fortinsylvain/MyCpu/Kicad/MyCpu_AddressData.kicad_sch

## KiCad design Kicad/MyCpu_AddressData.kicad_sch (2025-06-30)

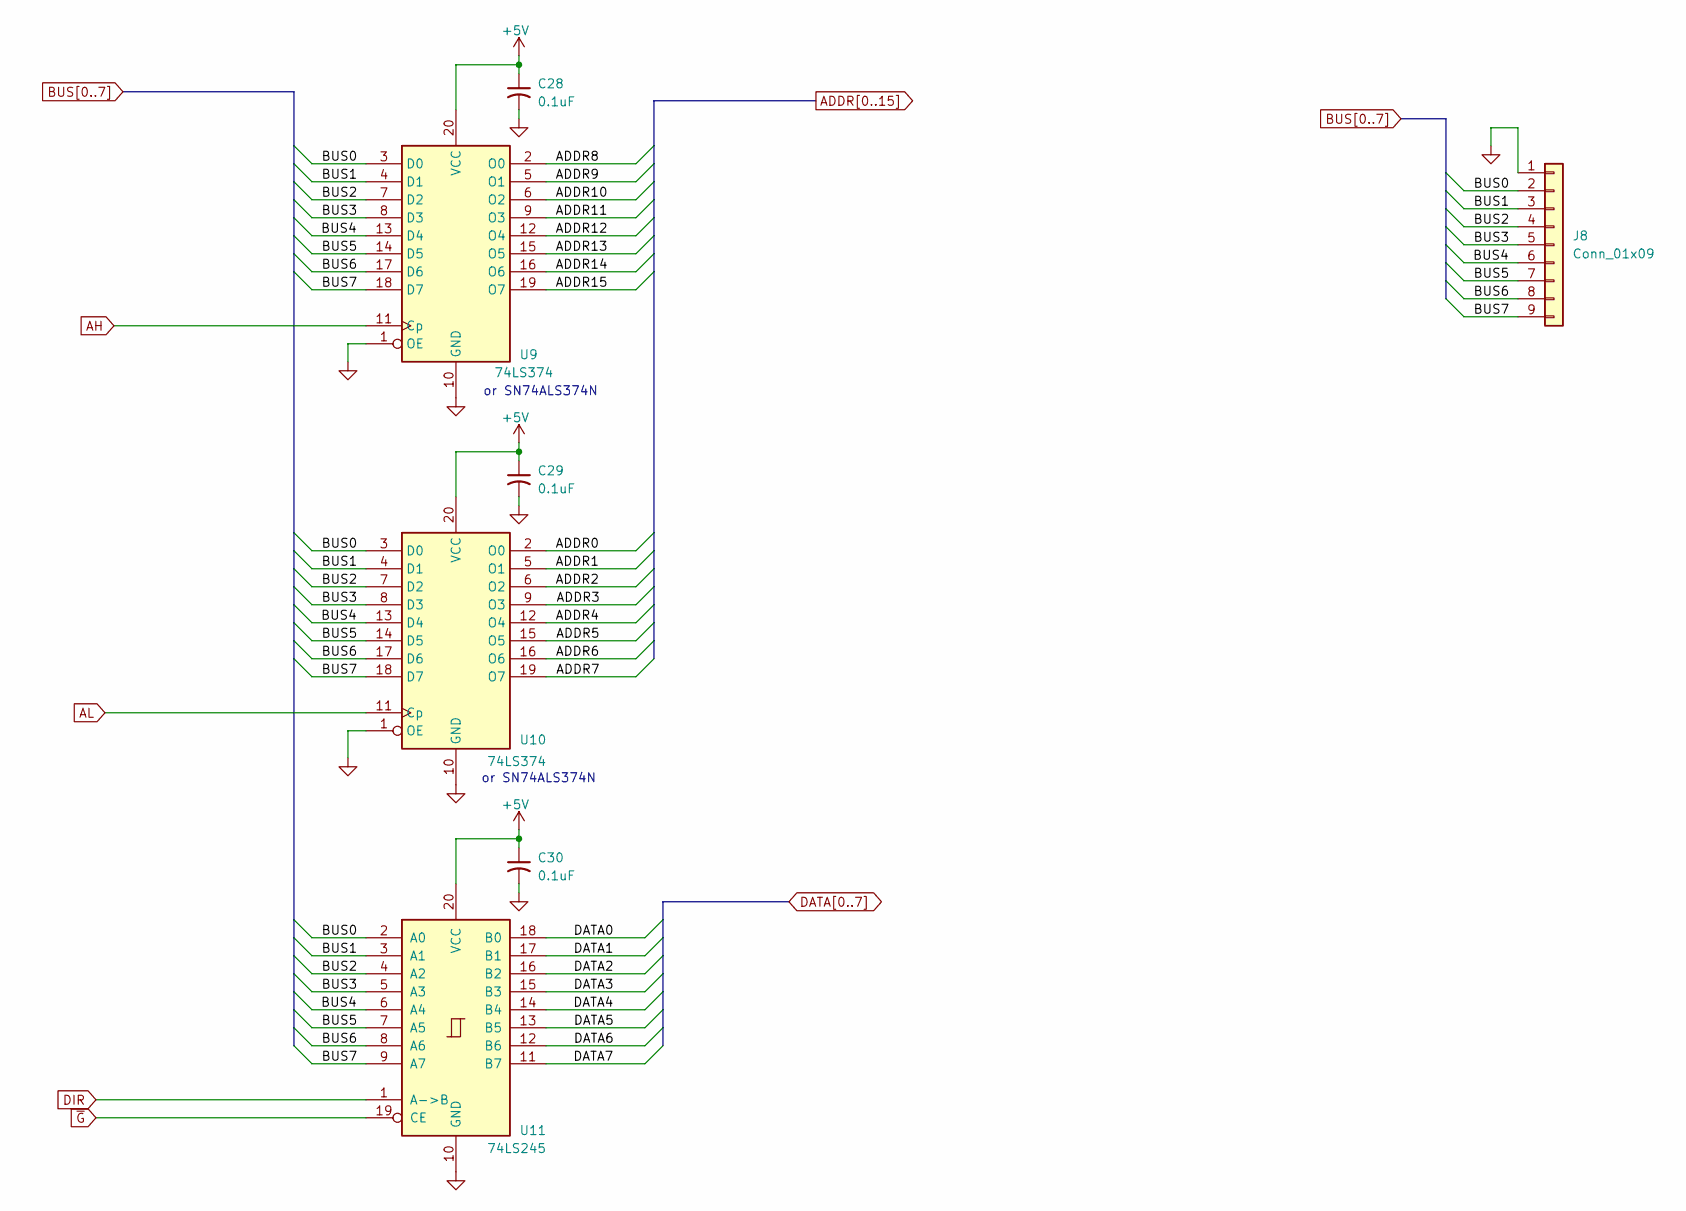
[picture p20: schematic MyCpu_AddressData.kicad_sch]

Parts:
C28, C29, C30: 0.1uF; C_Disc_D6.0mm_W2.5mm_P5.00mm
J8: Conn_01x09; PinHeader_1x09_P2.54mm_Vertical
U9, U10: 74LS374; DIP-20_W7.62mm_Socket_LongPads
U11: 74LS245; DIP-20_W7.62mm_Socket_LongPads

Connections:
+5V: C28.1, C29.1, C30.1, U9.20 (VCC), U10.20 (VCC), U11.20 (VCC)
ADDR0: U10.2 (O0)
ADDR1: U10.5 (O1)
ADDR2: U10.6 (O2)
ADDR3: U10.9 (O3)
ADDR4: U10.12 (O4)
ADDR5: U10.15 (O5)
ADDR6: U10.16 (O6)
ADDR7: U10.19 (O7)
ADDR8: U9.2 (O0)
ADDR9: U9.5 (O1)
ADDR10: U9.6 (O2)
ADDR11: U9.9 (O3)
ADDR12: U9.12 (O4)
ADDR13: U9.15 (O5)
ADDR14: U9.16 (O6)
ADDR15: U9.19 (O7)
AH: U9.11 (Cp)
AL: U10.11 (Cp)
BUS0: J8.2, U9.3 (D0), U10.3 (D0), U11.2 (A0)
BUS1: J8.3, U9.4 (D1), U10.4 (D1), U11.3 (A1)
BUS2: J8.4, U9.7 (D2), U10.7 (D2), U11.4 (A2)
BUS3: J8.5, U9.8 (D3), U10.8 (D3), U11.5 (A3)
BUS4: J8.6, U9.13 (D4), U10.13 (D4), U11.6 (A4)
BUS5: J8.7, U9.14 (D5), U10.14 (D5), U11.7 (A5)
BUS6: J8.8, U9.17 (D6), U10.17 (D6), U11.8 (A6)
BUS7: J8.9, U9.18 (D7), U10.18 (D7), U11.9 (A7)
DATA0: U11.18 (B0)
DATA1: U11.17 (B1)
DATA2: U11.16 (B2)
DATA3: U11.15 (B3)
DATA4: U11.14 (B4)
DATA5: U11.13 (B5)
DATA6: U11.12 (B6)
DATA7: U11.11 (B7)
DIR: U11.1 (A->B)
GND: C28.2, C29.2, C30.2, J8.1, U9.1 (OE), U9.10 (GND), U10.1 (OE), U10.10 (GND), U11.10 (GND)
~G: U11.19 (CE)

Notes on the sheet:
or SN74ALS374N
