fortinsylvain/MyCpu/Kicad/MyCpu_Alu.kicad_sch

## KiCad design Kicad/MyCpu_Alu.kicad_sch (2025-06-30)

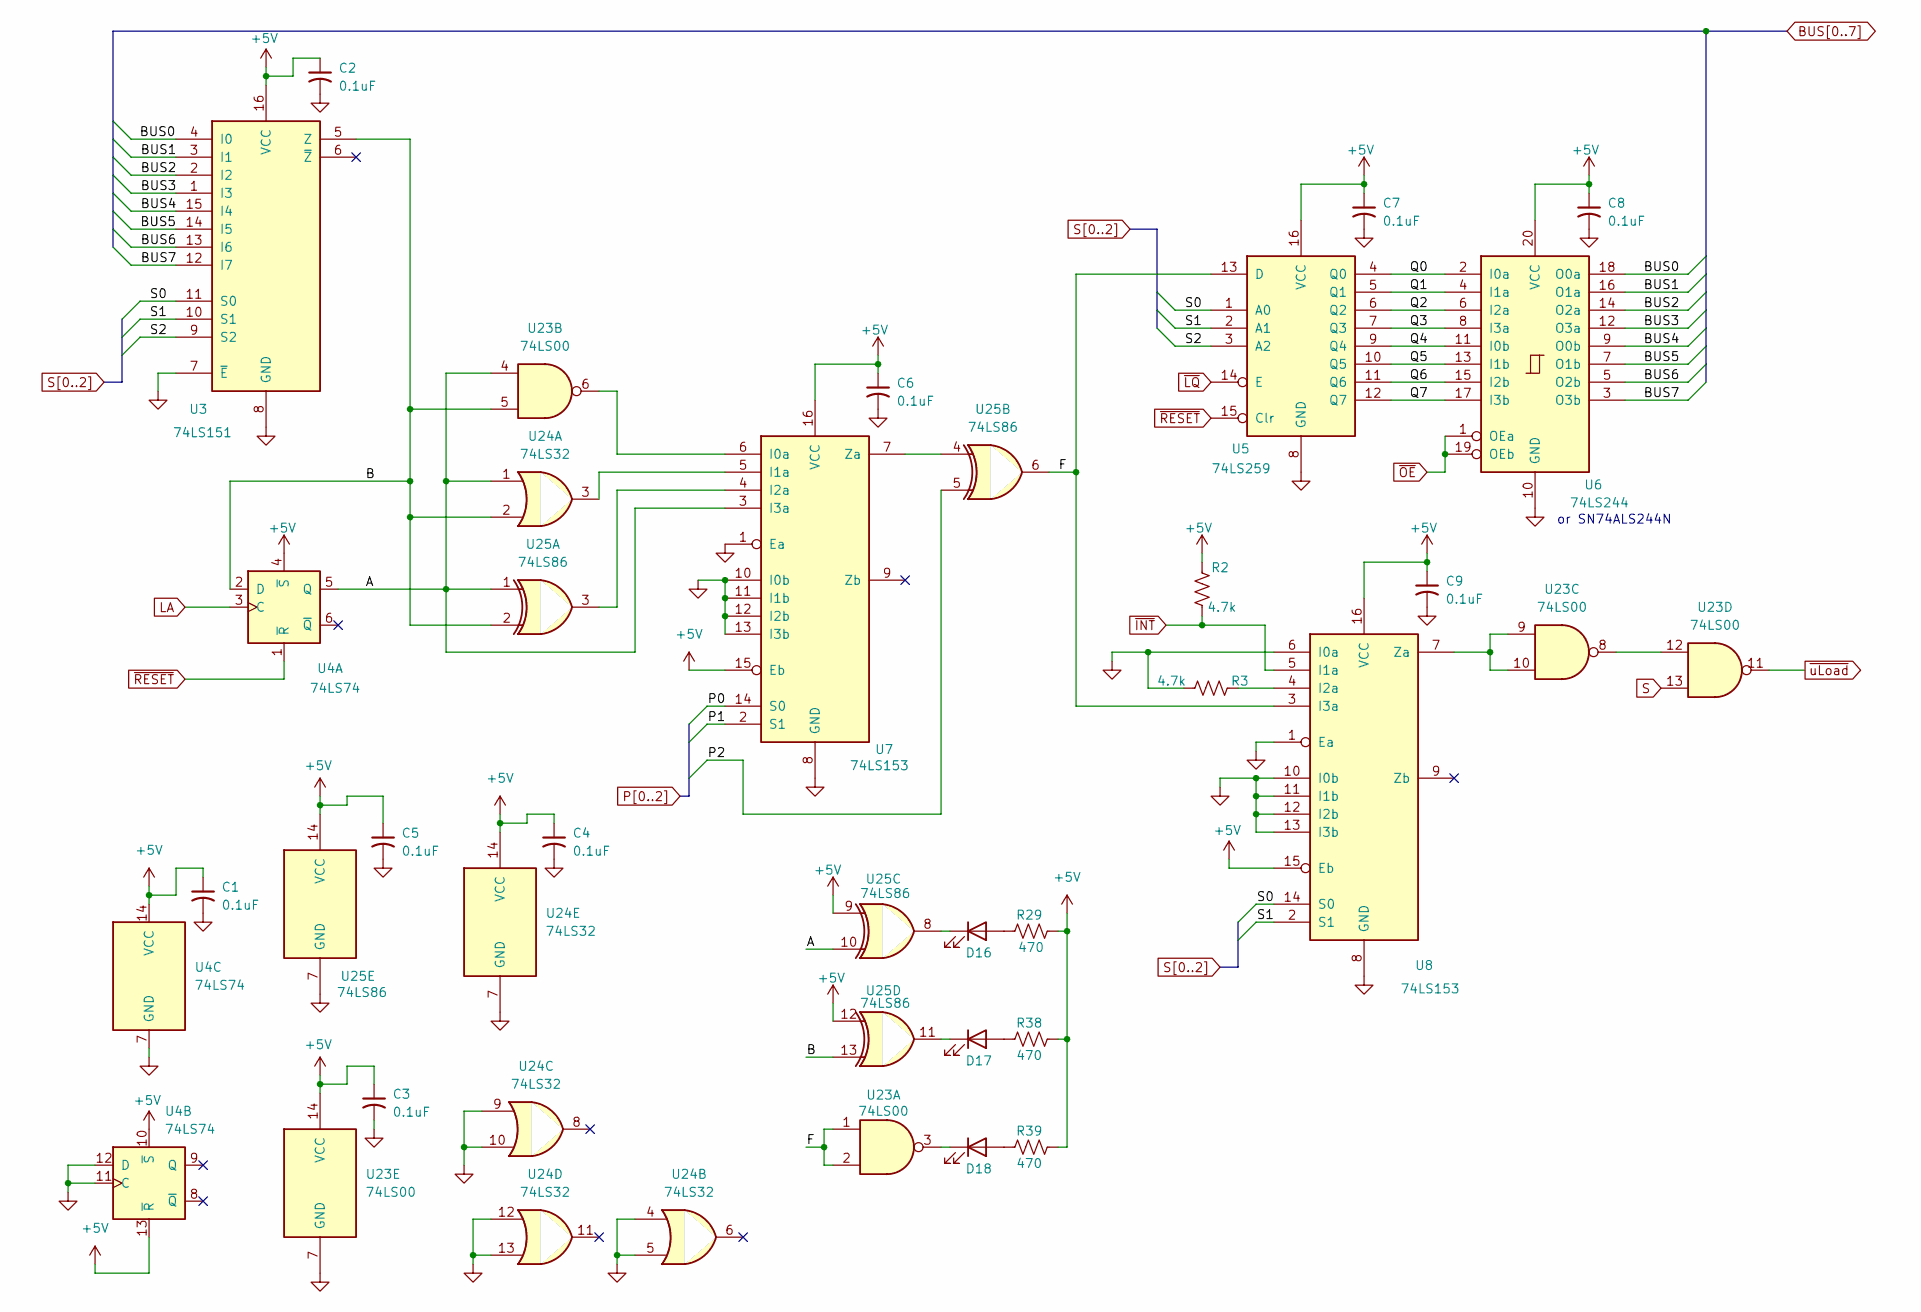
[picture p21: schematic MyCpu_Alu.kicad_sch]

Parts:
C1, C2, C3, C4, C5, C6, C7, C8, C9: 0.1uF; C_Disc_D6.0mm_W2.5mm_P5.00mm
D16, D17, D18: LED; LED_D5.0mm
R2, R3: 4.7k; R_Axial_DIN0207_L6.3mm_D2.5mm_P2.54mm_Vertical
R29, R38, R39: 470; R_Axial_DIN0207_L6.3mm_D2.5mm_P2.54mm_Vertical
U3: 74LS151; DIP-16_W7.62mm_Socket_LongPads
U4: 74LS74; DIP-14_W7.62mm_Socket_LongPads
U5: 74LS259; DIP-16_W7.62mm_Socket_LongPads
U6: 74LS244; DIP-20_W7.62mm_Socket_LongPads
U7, U8: 74LS153; DIP-16_W7.62mm_Socket_LongPads
U23: 74LS00; DIP-14_W7.62mm_Socket_LongPads
U24: 74LS32; DIP-14_W7.62mm_Socket_LongPads
U25: 74LS86; DIP-14_W7.62mm_Socket_LongPads

Connections:
+5V: C1.1, C2.1, C3.1, C4.1, C5.1, C6.1, C7.1, C8.1, C9.1, R2.1, R29.1, R38.1, R39.1, U3.16 (VCC), U4.4 (~S), U4.10 (~S), U4.13 (~R), U4.14 (VCC), U5.16 (VCC), U6.20 (VCC), U7.15 (Eb), U7.16 (VCC), U8.15 (Eb), U8.16 (VCC), U23.14 (VCC), U24.14 (VCC), U25.9, U25.12, U25.14 (VCC)
A: U4.5 (Q), U7.3 (I3a), U23.4, U24.1, U25.1, U25.10
B: U3.5 (Z), U4.2 (D), U23.5, U24.2, U25.2, U25.13
BUS0: U3.4 (I0), U6.18 (O0a)
BUS1: U3.3 (I1), U6.16 (O1a)
BUS2: U3.2 (I2), U6.14 (O2a)
BUS3: U3.1 (I3), U6.12 (O3a)
BUS4: U3.15 (I4), U6.9 (O0b)
BUS5: U3.14 (I5), U6.7 (O1b)
BUS6: U3.13 (I6), U6.5 (O2b)
BUS7: U3.12 (I7), U6.3 (O3b)
F: U5.13 (D), U8.3 (I3a), U23.1, U23.2, U25.6
GND: C1.2, C2.2, C3.2, C4.2, C5.2, C6.2, C7.2, C8.2, C9.2, R3.1, U3.7 (~E), U3.8 (GND), U4.7 (GND), U4.11 (C), U4.12 (D), U5.8 (GND), U6.10 (GND), U7.1 (Ea), U7.8 (GND), U7.10 (I0b), U7.11 (I1b), U7.12 (I2b), U7.13 (I3b), U8.1 (Ea), U8.6 (I0a), U8.8 (GND), U8.10 (I0b), U8.11 (I1b), U8.12 (I2b), U8.13 (I3b), U23.7 (GND), U24.4, U24.5, U24.7 (GND), U24.9, U24.10, U24.12, U24.13, U25.7 (GND)
LA: U4.3 (C)
unnamed: D16.1 (K), U25.8
unnamed: D16.2 (A), R29.2
unnamed: D17.1 (K), U25.11
unnamed: D17.2 (A), R38.2
unnamed: D18.1 (K), U23.3
unnamed: D18.2 (A), R39.2
unnamed: R3.2, U8.4 (I2a)
unnamed: U7.6 (I0a), U23.6
unnamed: U8.7 (Za), U23.9, U23.10
unnamed: U23.8, U23.12
unnamed: U7.5 (I1a), U24.3
unnamed: U7.4 (I2a), U25.3
unnamed: U7.7 (Za), U25.4
P0: U7.14 (S0)
P1: U7.2 (S1)
P2: U25.5
Q0: U5.4 (Q0), U6.2 (I0a)
Q1: U5.5 (Q1), U6.4 (I1a)
Q2: U5.6 (Q2), U6.6 (I2a)
Q3: U5.7 (Q3), U6.8 (I3a)
Q4: U5.9 (Q4), U6.11 (I0b)
Q5: U5.10 (Q5), U6.13 (I1b)
Q6: U5.11 (Q6), U6.15 (I2b)
Q7: U5.12 (Q7), U6.17 (I3b)
S: U23.13
S0: U3.11 (S0), U5.1 (A0), U8.14 (S0)
S1: U3.10 (S1), U5.2 (A1), U8.2 (S1)
S2: U3.9 (S2), U5.3 (A2)
~INT: R2.2, U8.5 (I1a)
~LQ: U5.14 (E)
~OE: U6.1 (OEa), U6.19 (OEb)
~RESET: U4.1 (~R), U5.15 (Clr)
~uLoad: U23.11

Notes on the sheet:
or SN74ALS244N
