fortinsylvain/MyCpu/Kicad/MyCpu_Clock.kicad_sch

## KiCad design Kicad/MyCpu_Clock.kicad_sch (2025-06-30)

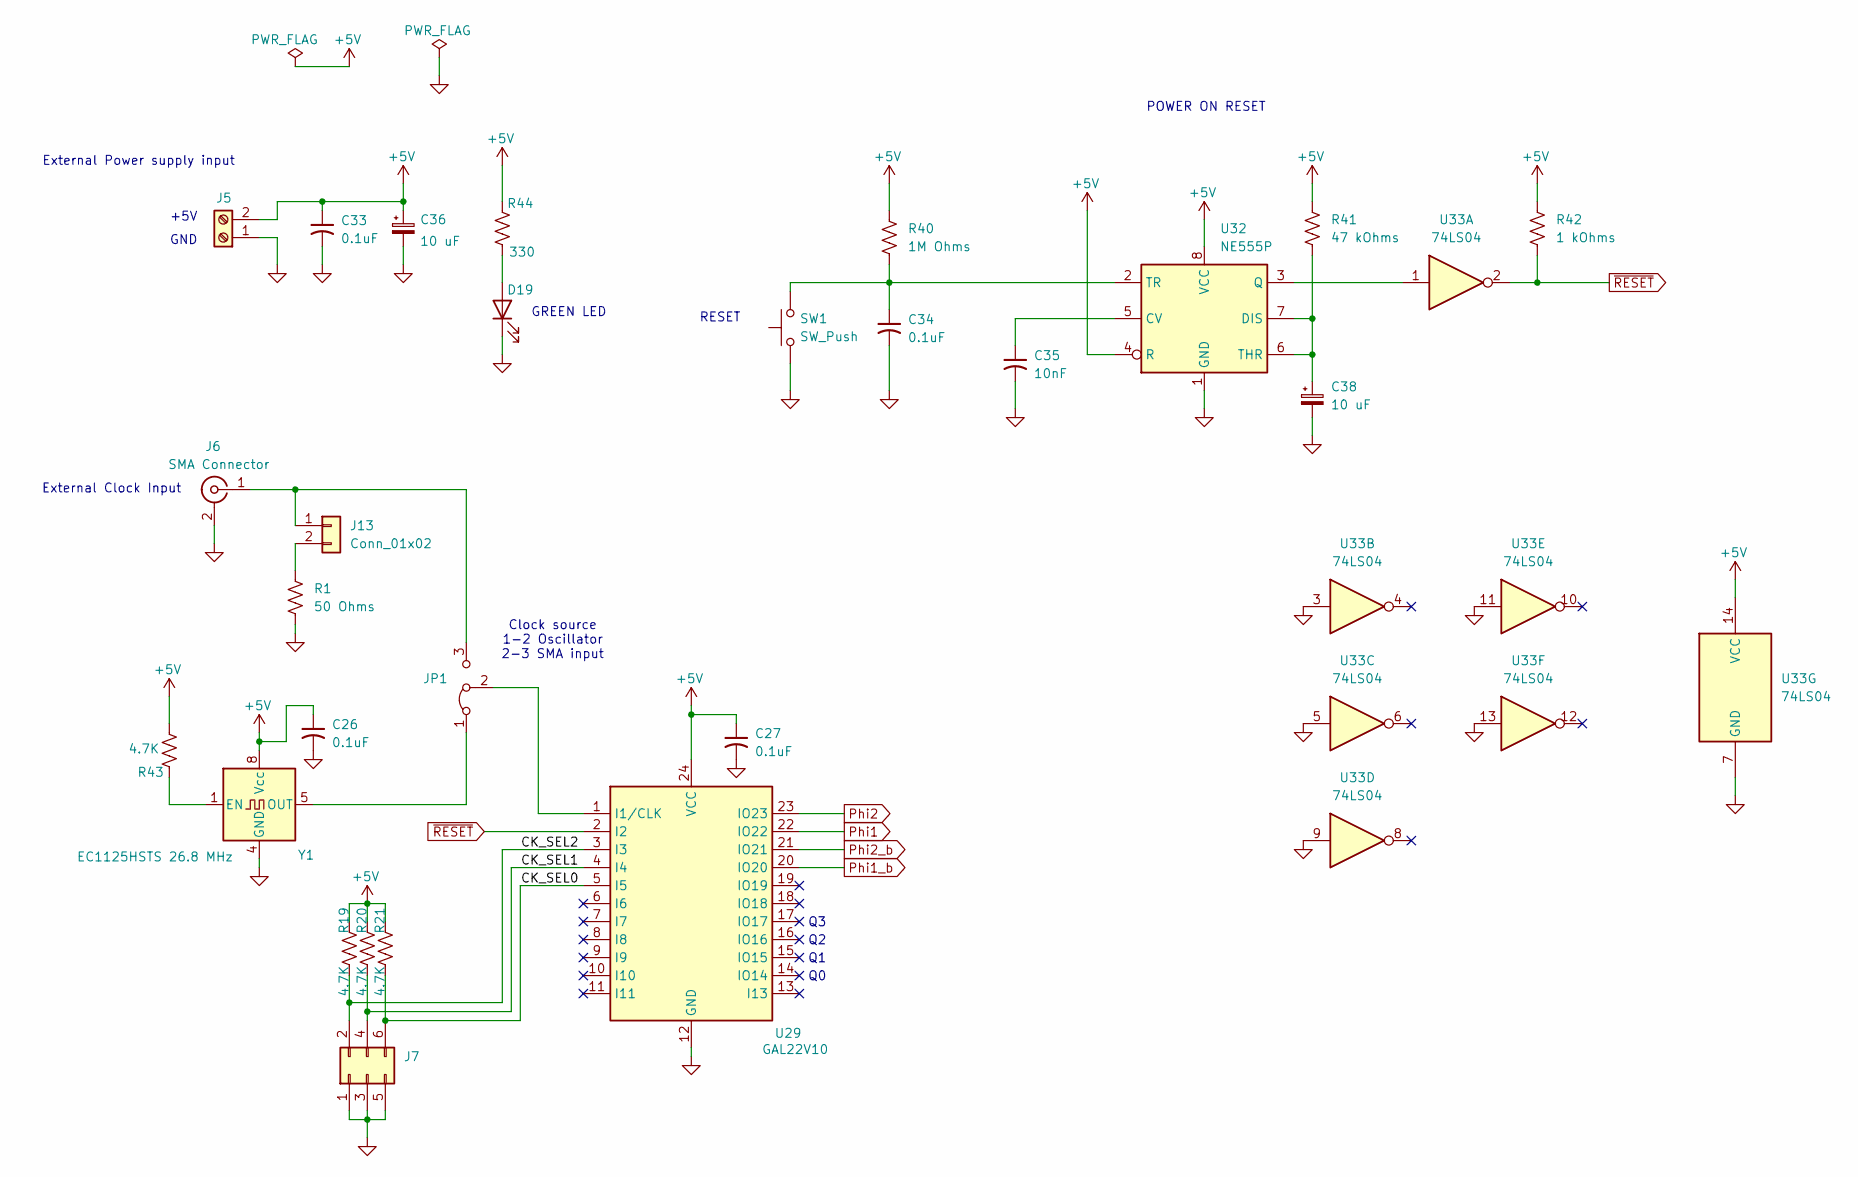
[picture p22: schematic MyCpu_Clock.kicad_sch]

Parts:
C26, C27, C33, C34: 0.1uF; C_Disc_D6.0mm_W2.5mm_P5.00mm
C35: 10nF; C_Disc_D6.5mm_W2.1mm_P6.50mm
C36, C38: 10 uF; CP_Radial_D5.0mm_P2.50mm
D19: LED; LED_D5.0mm
J5: Screw_Terminal_01x02; TerminalBlock_CUI_TB007-508-02_1x02_P5.08mm_Horizontal
J6: SMA Connector; GSG-SMA-73251-2120_drill_0.5mm
J7: Conn_02x03_Odd_Even; PinHeader_2x03_P2.54mm_Vertical
J13: Conn_01x02; PinHeader_1x02_P2.54mm_Vertical
JP1: Jumper_3_Bridged12; PinHeader_1x03_P2.54mm_Vertical
R1: 50 Ohms; R_Axial_DIN0207_L6.3mm_D2.5mm_P2.54mm_Vertical
R19, R20, R21, R43: 4.7K; R_Axial_DIN0207_L6.3mm_D2.5mm_P2.54mm_Vertical
R40: 1M Ohms; R_Axial_DIN0207_L6.3mm_D2.5mm_P2.54mm_Vertical
R41: 47 kOhms; R_Axial_DIN0207_L6.3mm_D2.5mm_P2.54mm_Vertical
R42: 1 kOhms; R_Axial_DIN0207_L6.3mm_D2.5mm_P2.54mm_Vertical
R44: 330; R_Axial_DIN0207_L6.3mm_D2.5mm_P2.54mm_Vertical
SW1: SW_Push; SW_PUSH-12mm
U29: GAL22V10; DIP-24_W7.62mm_Socket_LongPads
U32: NE555P; DIP-8_W7.62mm_Socket_LongPads
U33: 74LS04; DIP-14_W7.62mm_Socket_LongPads
Y1: EC1125HSTS 26.8 MHz; Oscillator_DIP-8

Connections:
+5V: C26.1, C27.1, C33.1, C36.1, J5.2, R19.1, R20.1, R21.1, R40.1, R41.1, R42.1, R43.1, R44.1, U29.24 (VCC), U32.4 (R), U32.8 (VCC), U33.14 (VCC), Y1.8 (Vcc)
CK_SEL0: J7.6, R21.2, U29.5 (I5)
CK_SEL1: J7.4, R20.2, U29.4 (I4)
CK_SEL2: J7.2, R19.2, U29.3 (I3)
GND: C26.2, C27.2, C33.2, C34.2, C35.2, C36.2, C38.2, D19.1 (K), J5.1, J6.2 (Ext), J7.1, J7.3, J7.5, R1.2, SW1.1, U29.12 (GND), U32.1 (GND), U33.3, U33.5, U33.7 (GND), U33.9, U33.11, U33.13, Y1.4 (GND)
unnamed: C34.1, R40.2, SW1.2, U32.2 (TR)
unnamed: C35.1, U32.5 (CV)
unnamed: C38.1, R41.2, U32.6 (THR), U32.7 (DIS)
unnamed: D19.2 (A), R44.2
unnamed: J6.1 (In), J13.1, JP1.3 (B)
unnamed: J13.2, R1.1
unnamed: JP1.1 (A), Y1.5 (OUT)
unnamed: JP1.2 (C), U29.1 (I1/CLK)
unnamed: R43.2, Y1.1 (EN)
unnamed: U32.3 (Q), U33.1
Phi1: U29.22 (IO22)
Phi1_b: U29.20 (IO20)
Phi2: U29.23 (IO23)
Phi2_b: U29.21 (IO21)
~RESET: R42.2, U29.2 (I2), U33.2

Notes on the sheet:
RESET
POWER ON RESET
GREEN LED
External Clock Input
+5V
GND
Clock source 1-2 Oscillator 2-3 SMA input
External Power supply input
