fortinsylvain/MyCpu/Kicad/MyCpu_EEPROM_ucode.kicad_sch

## KiCad design Kicad/MyCpu_EEPROM_ucode.kicad_sch (2025-06-30)

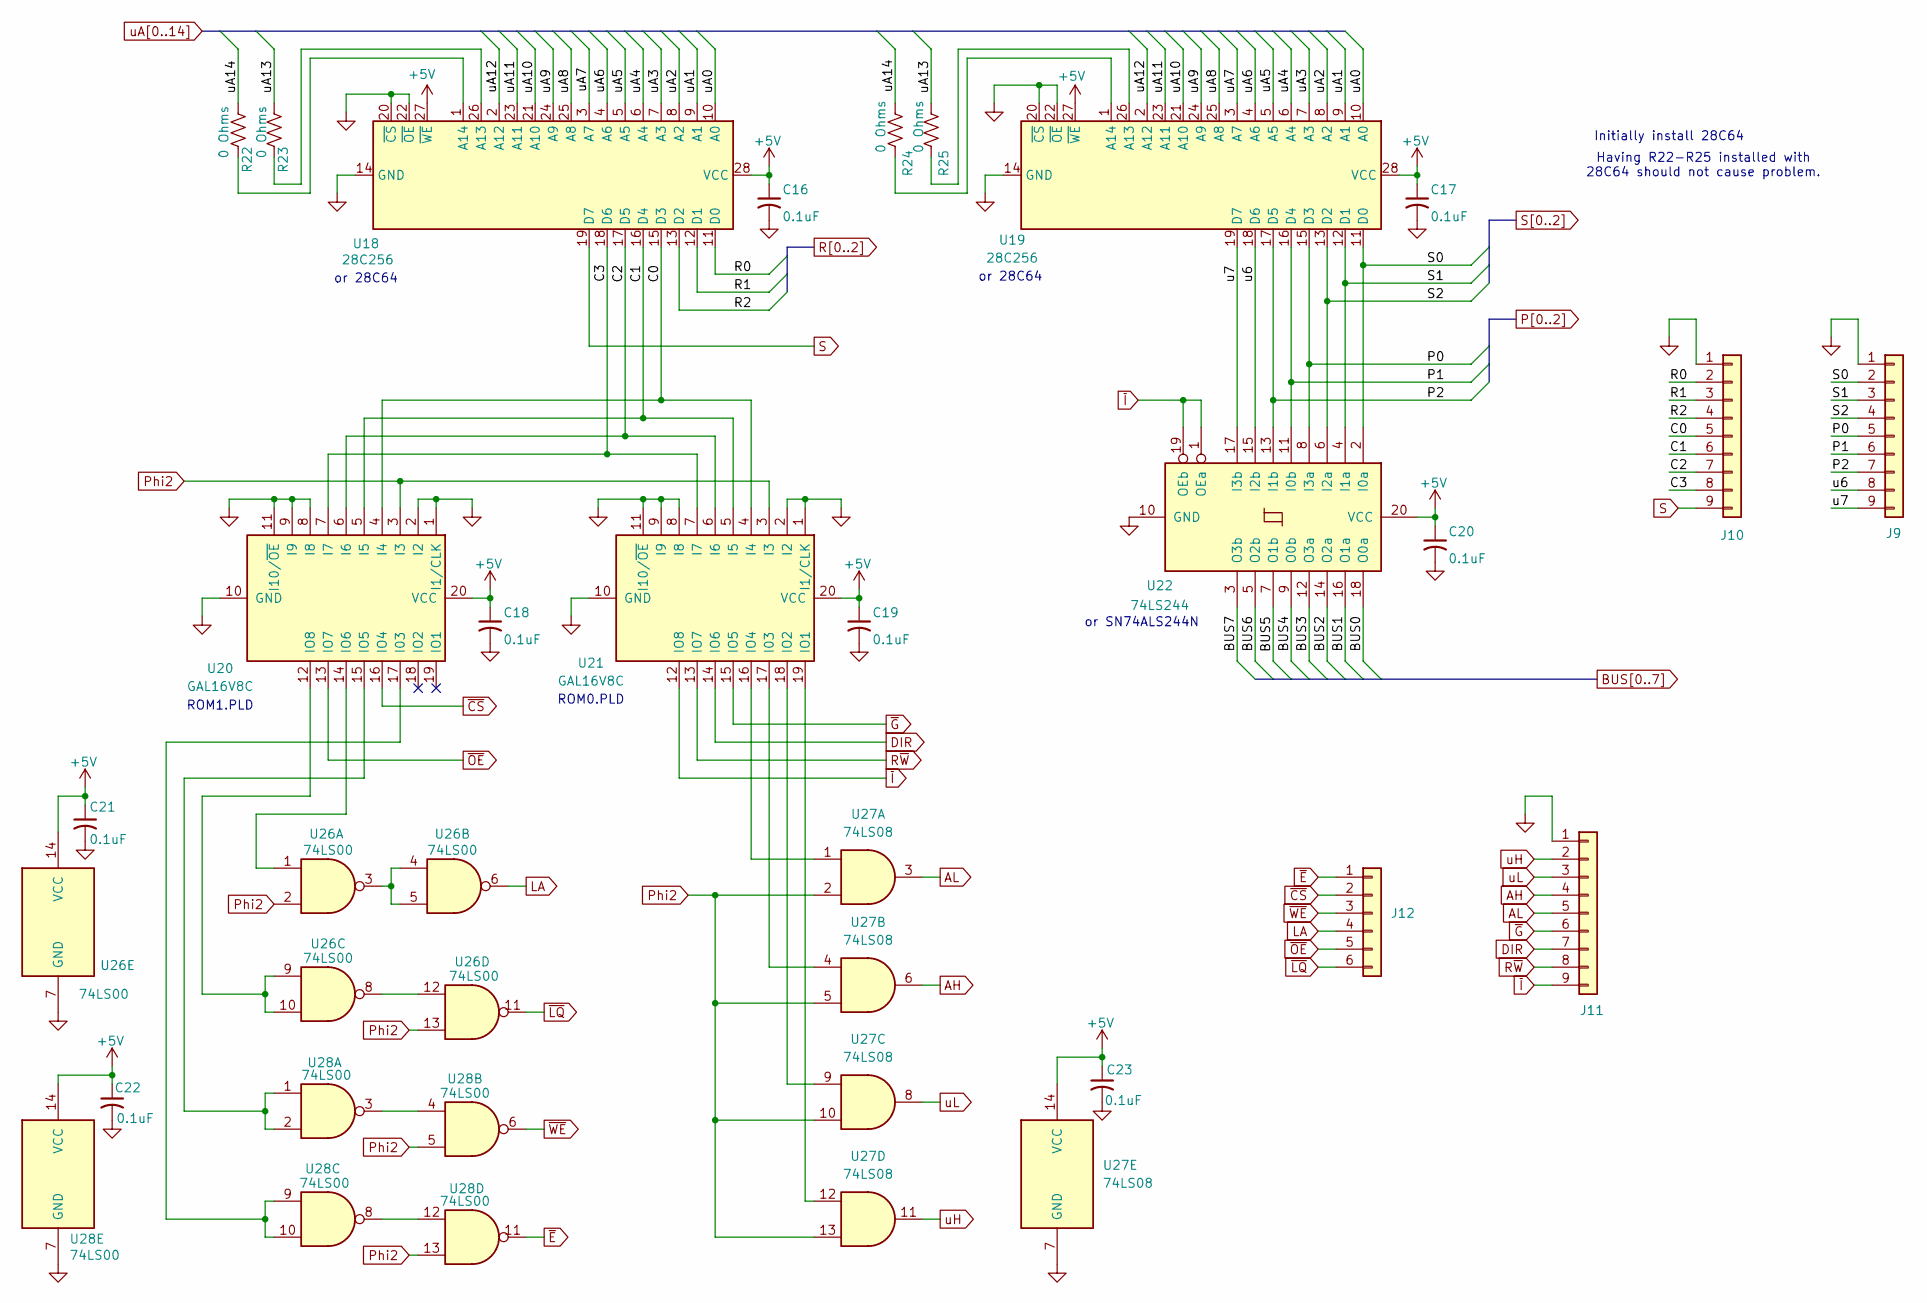
[picture p23: schematic MyCpu_EEPROM_ucode.kicad_sch]

Parts:
C16, C17, C18, C19, C20, C21, C22, C23: 0.1uF; C_Disc_D6.0mm_W2.5mm_P5.00mm
J9, J10, J11: Conn_01x09; PinHeader_1x09_P2.54mm_Vertical
J12: Conn_01x06; PinHeader_1x06_P2.54mm_Vertical
R22, R23, R24, R25: 0 Ohms; R_0603_1608Metric_Pad0.98x0.95mm_HandSolder
U18, U19: 28C256; DIP-28_W15.24mm_Socket_LongPads
U20, U21: GAL16V8C; DIP-20_W7.62mm_Socket_LongPads
U22: 74LS244; DIP-20_W7.62mm_Socket_LongPads
U26, U28: 74LS00; DIP-14_W7.62mm_Socket_LongPads
U27: 74LS08; DIP-14_W7.62mm_Socket_LongPads

Connections:
+5V: C16.1, C17.1, C18.1, C19.1, C20.1, C21.1, C22.1, C23.1, U18.27 (~WE), U18.28 (VCC), U19.27 (~WE), U19.28 (VCC), U20.20 (VCC), U21.20 (VCC), U22.20 (VCC), U26.14 (VCC), U27.14 (VCC), U28.14 (VCC)
AH: J11.4, U27.6
AL: J11.5, U27.3
BUS0: U22.18 (O0a)
BUS1: U22.16 (O1a)
BUS2: U22.14 (O2a)
BUS3: U22.12 (O3a)
BUS4: U22.9 (O0b)
BUS5: U22.7 (O1b)
BUS6: U22.5 (O2b)
BUS7: U22.3 (O3b)
C0: J10.5, U18.15 (D3), U20.4 (I4), U21.4 (I4)
C1: J10.6, U18.16 (D4), U20.5 (I5), U21.5 (I5)
C2: J10.7, U18.17 (D5), U20.6 (I6), U21.6 (I6)
C3: J10.8, U18.18 (D6), U20.7 (I7), U21.7 (I7)
DIR: J11.7, U21.14 (IO6)
GND: C16.2, C17.2, C18.2, C19.2, C20.2, C21.2, C22.2, C23.2, J9.1, J10.1, J11.1, U18.14 (GND), U18.20 (~CS), U18.22 (~OE), U19.14 (GND), U19.20 (~CS), U19.22 (~OE), U20.1 (I1/CLK), U20.2 (I2), U20.8 (I8), U20.9 (I9), U20.10 (GND), U20.11 (I10/~OE), U21.1 (I1/CLK), U21.2 (I2), U21.8 (I8), U21.9 (I9), U21.10 (GND), U21.11 (I10/~OE), U22.10 (GND), U26.7 (GND), U27.7 (GND), U28.7 (GND)
LA: J12.4, U26.6
unnamed: R22.2, U18.1 (A14)
unnamed: R23.2, U18.26 (A13)
unnamed: R24.2, U19.1 (A14)
unnamed: R25.2, U19.26 (A13)
unnamed: U20.12 (IO8), U26.9, U26.10
unnamed: U20.14 (IO6), U26.1
unnamed: U20.15 (IO5), U28.1, U28.2
unnamed: U20.17 (I03), U28.9, U28.10
unnamed: U21.16 (IO4), U27.1
unnamed: U21.17 (I03), U27.4
unnamed: U21.18 (IO2), U27.9
unnamed: U21.19 (IO1), U27.12
unnamed: U26.3, U26.4, U26.5
unnamed: U26.8, U26.12
unnamed: U28.3, U28.4
unnamed: U28.8, U28.12
P0: J9.5, U19.15 (D3), U22.8 (I3a)
P1: J9.6, U19.16 (D4), U22.11 (I0b)
P2: J9.7, U19.17 (D5), U22.13 (I1b)
Phi2: U20.3 (I3), U21.3 (I3), U26.2, U26.13, U27.2, U27.5, U27.10, U27.13, U28.5, U28.13
R0: J10.2, U18.11 (D0)
R1: J10.3, U18.12 (D1)
R2: J10.4, U18.13 (D2)
R~W: J11.8, U21.13 (IO7)
S: J10.9, U18.19 (D7)
S0: J9.2, U19.11 (D0), U22.2 (I0a)
S1: J9.3, U19.12 (D1), U22.4 (I1a)
S2: J9.4, U19.13 (D2), U22.6 (I2a)
u6: J9.8, U19.18 (D6), U22.15 (I2b)
u7: J9.9, U19.19 (D7), U22.17 (I3b)
uA0: U18.10 (A0), U19.10 (A0)
uA1: U18.9 (A1), U19.9 (A1)
uA2: U18.8 (A2), U19.8 (A2)
uA3: U18.7 (A3), U19.7 (A3)
uA4: U18.6 (A4), U19.6 (A4)
uA5: U18.5 (A5), U19.5 (A5)
uA6: U18.4 (A6), U19.4 (A6)
uA7: U18.3 (A7), U19.3 (A7)
uA8: U18.25 (A8), U19.25 (A8)
uA9: U18.24 (A9), U19.24 (A9)
uA10: U18.21 (A10), U19.21 (A10)
uA11: U18.23 (A11), U19.23 (A11)
uA12: U18.2 (A12), U19.2 (A12)
uA13: R23.1, R25.1
uA14: R22.1, R24.1
uH: J11.2, U27.11
uL: J11.3, U27.8
~CS: J12.2, U20.16 (IO4)
~E: J12.1, U28.11
~G: J11.6, U21.15 (IO5)
~I: J11.9, U21.12 (IO8), U22.1 (OEa), U22.19 (OEb)
~LQ: J12.6, U26.11
~OE: J12.5, U20.13 (IO7)
~WE: J12.3, U28.6

Notes on the sheet:
Initially install 28C64
ROM0.PLD
Having R22-R25 installed with 28C64 should not cause problem.
ROM1.PLD
or 28C64
or SN74ALS244N
