fortinsylvain/MyCpu/Kicad/MyCpu_ProgramRamEeprom.kicad_sch

## KiCad design Kicad/MyCpu_ProgramRamEeprom.kicad_sch (2025-06-30)

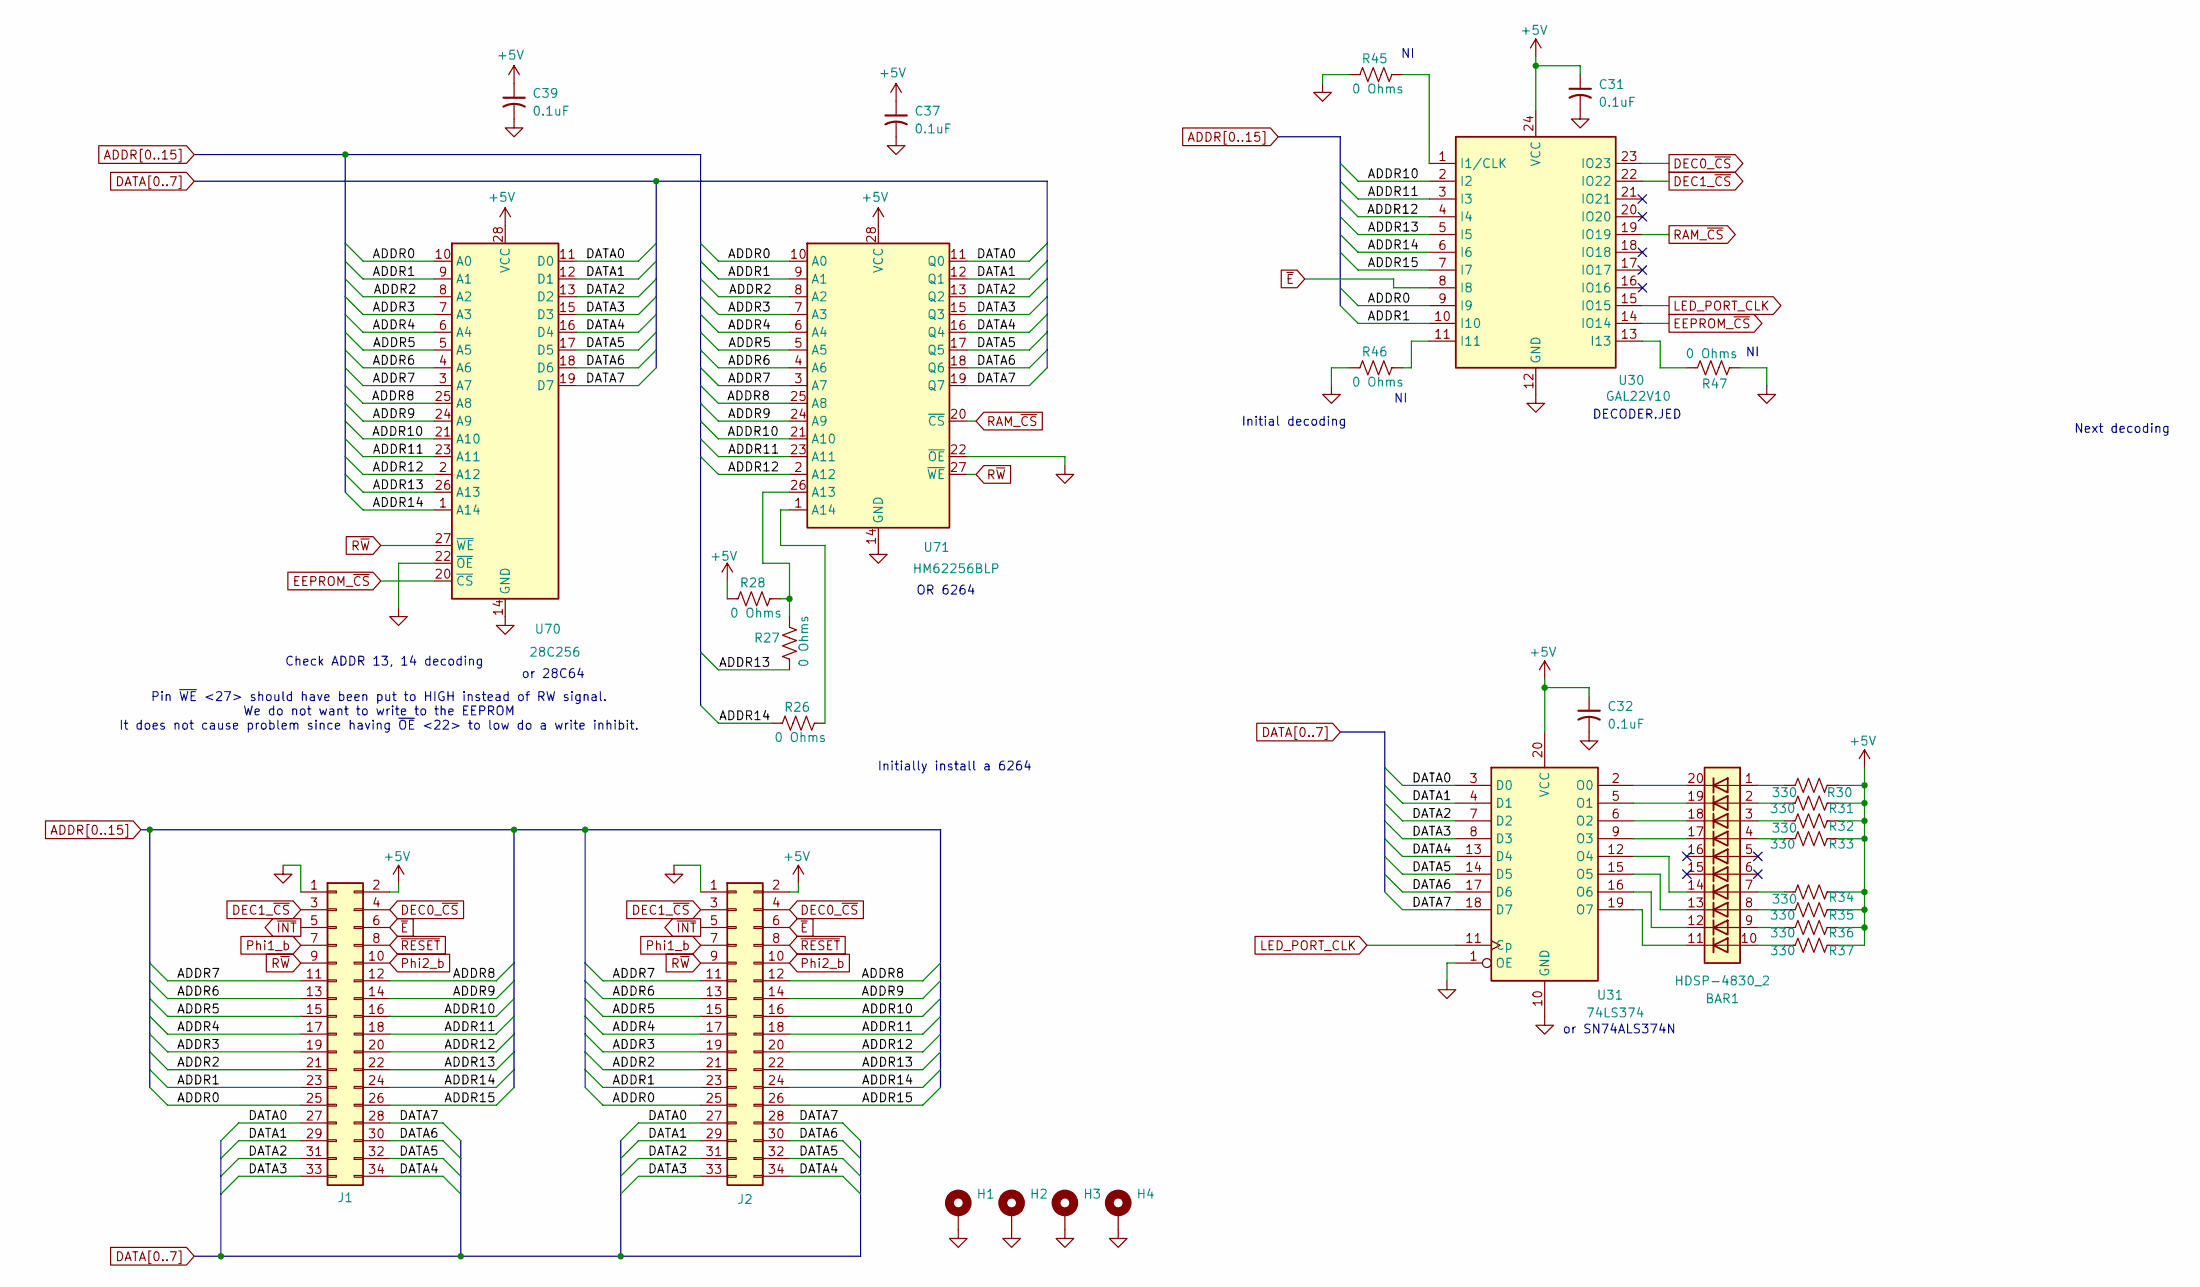
[picture p24: schematic MyCpu_ProgramRamEeprom.kicad_sch]

Parts:
BAR1: HDSP-4830_2; HDSP-4830
C31, C32, C37, C39: 0.1uF; C_Disc_D6.0mm_W2.5mm_P5.00mm
H1, H2, H3, H4: MountingHole_Pad; MountingHole_3.2mm_M3_Pad_Via_Drill_0.5mm
J1, J2: Conn_02x17_Odd_Even; PinHeader_2x17_P2.54mm_Vertical
R26, R27, R28, R45, R46, R47: 0 Ohms; R_0603_1608Metric_Pad0.98x0.95mm_HandSolder
R30, R31, R32, R33, R34, R35, R36, R37: 330; R_Axial_DIN0207_L6.3mm_D2.5mm_P2.54mm_Vertical
U30: GAL22V10; DIP-24_W7.62mm_Socket_LongPads
U31: 74LS374; DIP-20_W7.62mm_Socket_LongPads
U70: 28C256; DIP-28_W15.24mm_Socket_LongPads
U71: HM62256BLP; DIP-28_W15.24mm_Socket_LongPads

Connections:
+5V: C31.1, C32.1, C37.1, C39.1, J1.2, J2.2, R28.1, R30.1, R31.1, R32.1, R33.1, R34.1, R35.1, R36.1, R37.1, U30.24 (VCC), U31.20 (VCC), U70.28 (VCC), U71.28 (VCC)
ADDR0: J1.25, J2.25, U30.9 (I9), U70.10 (A0), U71.10 (A0)
ADDR1: J1.23, J2.23, U30.10 (I10), U70.9 (A1), U71.9 (A1)
ADDR2: J1.21, J2.21, U70.8 (A2), U71.8 (A2)
ADDR3: J1.19, J2.19, U70.7 (A3), U71.7 (A3)
ADDR4: J1.17, J2.17, U70.6 (A4), U71.6 (A4)
ADDR5: J1.15, J2.15, U70.5 (A5), U71.5 (A5)
ADDR6: J1.13, J2.13, U70.4 (A6), U71.4 (A6)
ADDR7: J1.11, J2.11, U70.3 (A7), U71.3 (A7)
ADDR8: J1.12, J2.12, U70.25 (A8), U71.25 (A8)
ADDR9: J1.14, J2.14, U70.24 (A9), U71.24 (A9)
ADDR10: J1.16, J2.16, U30.2 (I2), U70.21 (A10), U71.21 (A10)
ADDR11: J1.18, J2.18, U30.3 (I3), U70.23 (A11), U71.23 (A11)
ADDR12: J1.20, J2.20, U30.4 (I4), U70.2 (A12), U71.2 (A12)
ADDR13: J1.22, J2.22, R27.1, U30.5 (I5), U70.26 (A13)
ADDR14: J1.24, J2.24, R26.1, U30.6 (I6), U70.1 (A14)
ADDR15: J1.26, J2.26, U30.7 (I7)
DATA0: J1.27, J2.27, U31.3 (D0), U70.11 (D0), U71.11 (Q0)
DATA1: J1.29, J2.29, U31.4 (D1), U70.12 (D1), U71.12 (Q1)
DATA2: J1.31, J2.31, U31.7 (D2), U70.13 (D2), U71.13 (Q2)
DATA3: J1.33, J2.33, U31.8 (D3), U70.15 (D3), U71.15 (Q3)
DATA4: J1.34, J2.34, U31.13 (D4), U70.16 (D4), U71.16 (Q4)
DATA5: J1.32, J2.32, U31.14 (D5), U70.17 (D5), U71.17 (Q5)
DATA6: J1.30, J2.30, U31.17 (D6), U70.18 (D6), U71.18 (Q6)
DATA7: J1.28, J2.28, U31.18 (D7), U70.19 (D7), U71.19 (Q7)
DEC0_~CS: J1.4, J2.4, U30.23 (IO23)
DEC1_~CS: J1.3, J2.3, U30.22 (IO22)
EEPROM_~CS: U30.14 (IO14), U70.20 (~CS)
GND: C31.2, C32.2, C37.2, C39.2, H1.1, H2.1, H3.1, H4.1, J1.1, J2.1, R45.1, R46.1, R47.1, U30.12 (GND), U31.1 (OE), U31.10 (GND), U70.14 (GND), U70.22 (~OE), U71.14 (GND), U71.22 (~OE)
LED_PORT_CLK: U30.15 (IO15), U31.11 (Cp)
unnamed: BAR1.1 (A), R30.2
unnamed: BAR1.2 (A), R31.2
unnamed: BAR1.3 (A), R32.2
unnamed: BAR1.4 (A), R33.2
unnamed: BAR1.7 (A), R34.2
unnamed: BAR1.8 (A), R35.2
unnamed: BAR1.9 (A), R36.2
unnamed: BAR1.10 (A), R37.2
unnamed: BAR1.11 (K), U31.19 (O7)
unnamed: BAR1.12 (K), U31.16 (O6)
unnamed: BAR1.13 (K), U31.15 (O5)
unnamed: BAR1.14 (K), U31.12 (O4)
unnamed: BAR1.17 (K), U31.9 (O3)
unnamed: BAR1.18 (K), U31.6 (O2)
unnamed: BAR1.19 (K), U31.5 (O1)
unnamed: BAR1.20 (K), U31.2 (O0)
unnamed: R26.2, U71.1 (A14)
unnamed: R27.2, R28.2, U71.26 (A13)
unnamed: R45.2, U30.1 (I1/CLK)
unnamed: R46.2, U30.11 (I11)
unnamed: R47.2, U30.13 (I13)
Phi1_b: J1.7, J2.7
Phi2_b: J1.10, J2.10
RAM_~CS: U30.19 (IO19), U71.20 (~CS)
R~W: J1.9, J2.9, U70.27 (~WE), U71.27 (~WE)
~E: J1.6, J2.6, U30.8 (I8)
~INT: J1.5, J2.5
~RESET: J1.8, J2.8

Notes on the sheet:
Pin ~{WE} <27> should have been put to HIGH instead of RW signal. We do not want to write to the EEPROM It does not cause problem since having ~{OE} <22> to low do a write inhibit.
or SN74ALS374N
Check ADDR 13, 14 decoding
or 28C64
Initially install a 6264
OR 6264
DECODER.JED
Initial decoding
Next decoding
