fortinsylvain/MyCpu/Kicad/MyCpu_Registers.kicad_sch

## KiCad design Kicad/MyCpu_Registers.kicad_sch (2025-06-30)

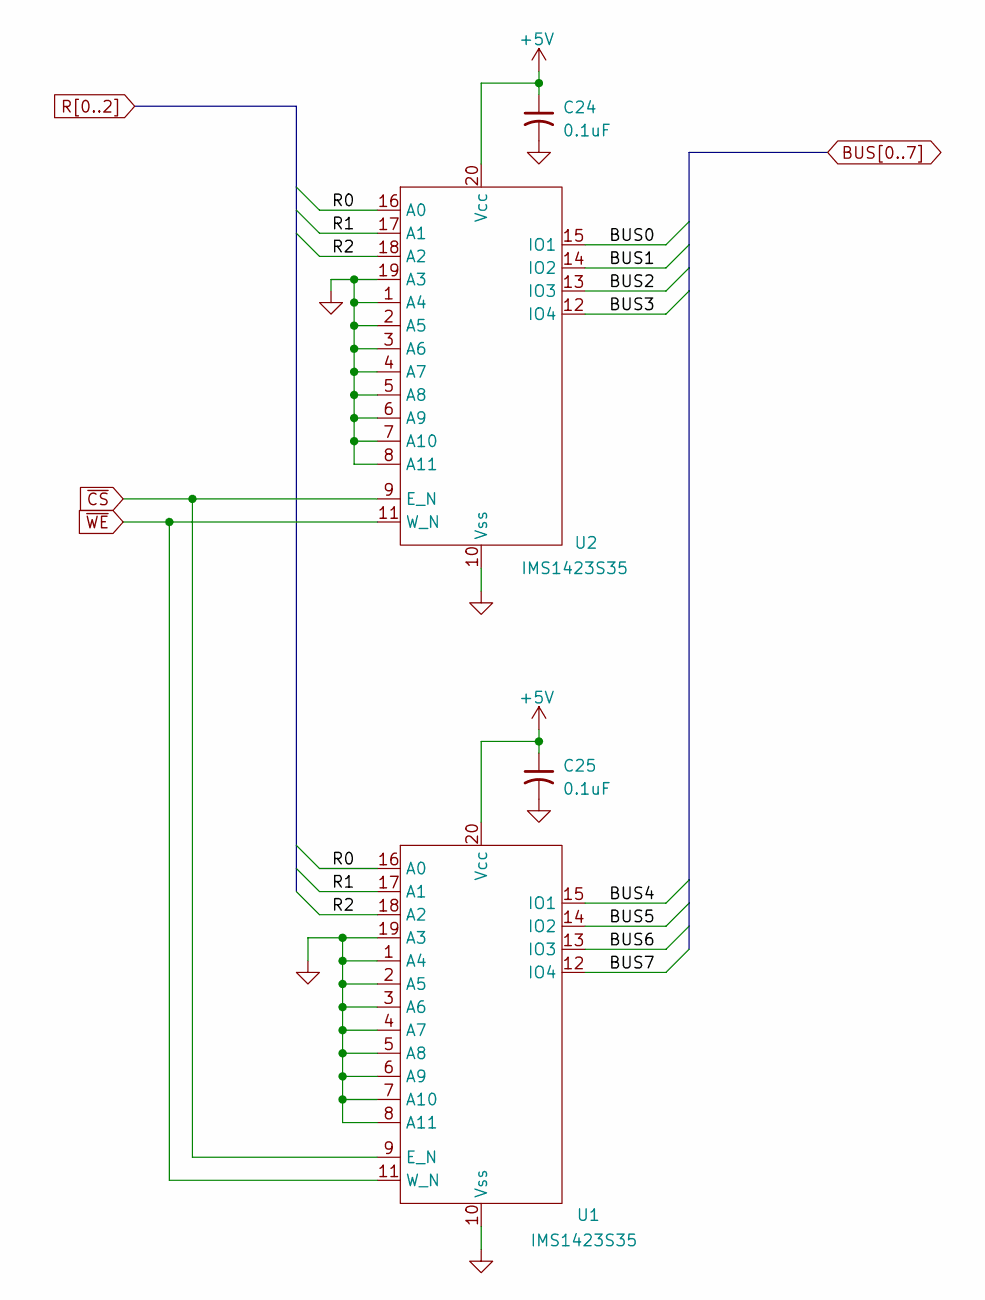
[picture p25: schematic MyCpu_Registers.kicad_sch]

Parts:
C24, C25: 0.1uF; C_Disc_D6.0mm_W2.5mm_P5.00mm
U1, U2: IMS1423S35; DIP-20_W7.62mm_Socket_LongPads

Connections:
+5V: C24.1, C25.1, U1.20 (Vcc), U2.20 (Vcc)
BUS0: U2.15 (IO1)
BUS1: U2.14 (IO2)
BUS2: U2.13 (IO3)
BUS3: U2.12 (IO4)
BUS4: U1.15 (IO1)
BUS5: U1.14 (IO2)
BUS6: U1.13 (IO3)
BUS7: U1.12 (IO4)
GND: C24.2, C25.2, U1.1 (A4), U1.2 (A5), U1.3 (A6), U1.4 (A7), U1.5 (A8), U1.6 (A9), U1.7 (A10), U1.8 (A11), U1.10 (Vss), U1.19 (A3), U2.1 (A4), U2.2 (A5), U2.3 (A6), U2.4 (A7), U2.5 (A8), U2.6 (A9), U2.7 (A10), U2.8 (A11), U2.10 (Vss), U2.19 (A3)
R0: U1.16 (A0), U2.16 (A0)
R1: U1.17 (A1), U2.17 (A1)
R2: U1.18 (A2), U2.18 (A2)
~CS: U1.9 (E_N), U2.9 (E_N)
~WE: U1.11 (W_N), U2.11 (W_N)
