fortinsylvain/MyCpu/Kicad/MyCpu_counter.kicad_sch

## KiCad design Kicad/MyCpu_counter.kicad_sch (2025-06-30)

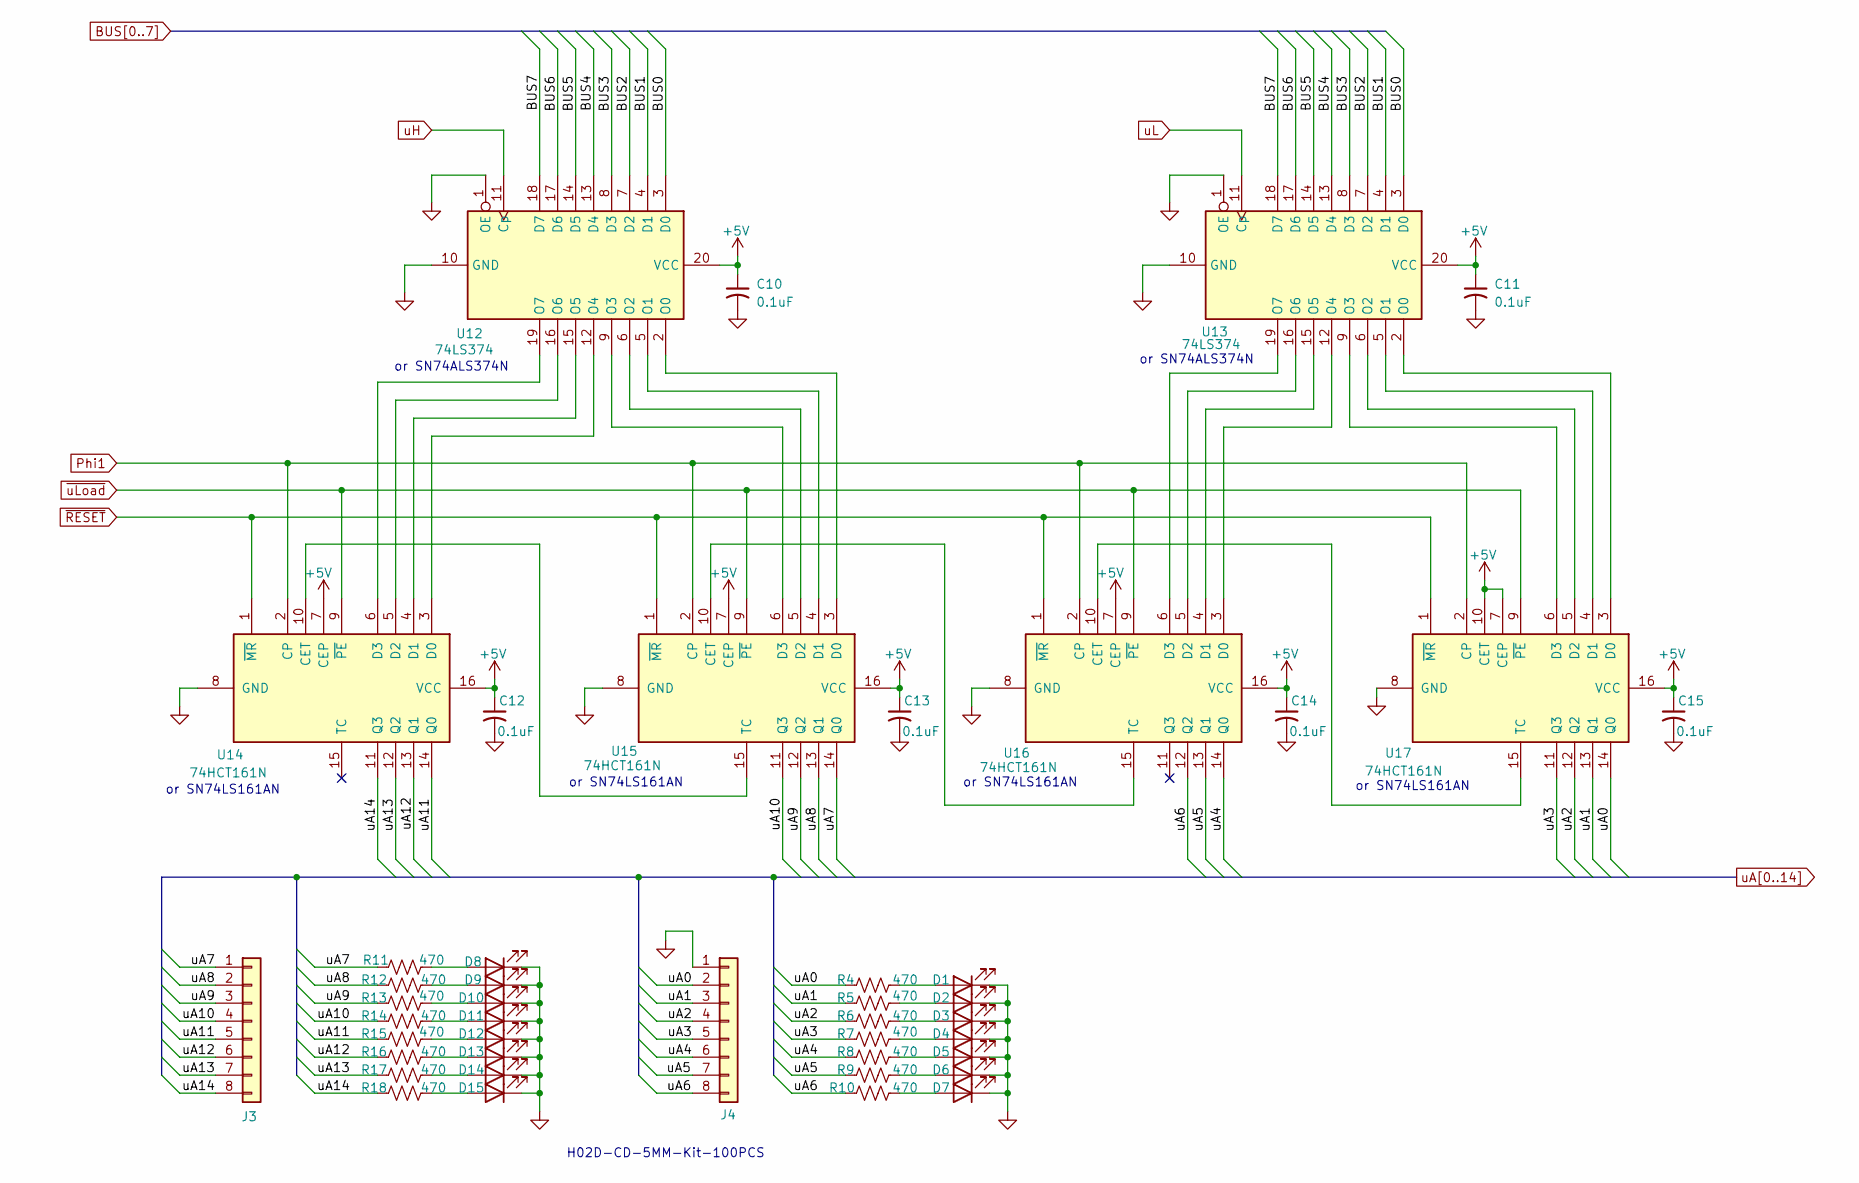
[picture p26: schematic MyCpu_counter.kicad_sch]

Parts:
C10, C11, C12, C13, C14, C15: 0.1uF; C_Disc_D6.0mm_W2.5mm_P5.00mm
D1, D2, D3, D4, D5, D6, D7, D8, D9, D10, D11, D12, D13, D14, D15: LED; LED_D5.0mm
J3, J4: Conn_01x08; PinHeader_1x08_P2.54mm_Vertical
R4, R5, R6, R7, R8, R9, R10, R11, R12, R13, R14, R15, R16, R17, R18: 470; R_Axial_DIN0207_L6.3mm_D2.5mm_P2.54mm_Vertical
U12, U13: 74LS374; DIP-20_W7.62mm_Socket_LongPads
U14, U15, U16, U17: 74HCT161N; DIP-16_W7.62mm_Socket_LongPads

Connections:
+5V: C10.1, C11.1, C12.1, C13.1, C14.1, C15.1, U12.20 (VCC), U13.20 (VCC), U14.7 (CEP), U14.16 (VCC), U15.7 (CEP), U15.16 (VCC), U16.7 (CEP), U16.16 (VCC), U17.7 (CEP), U17.10 (CET), U17.16 (VCC)
BUS0: U12.3 (D0), U13.3 (D0)
BUS1: U12.4 (D1), U13.4 (D1)
BUS2: U12.7 (D2), U13.7 (D2)
BUS3: U12.8 (D3), U13.8 (D3)
BUS4: U12.13 (D4), U13.13 (D4)
BUS5: U12.14 (D5), U13.14 (D5)
BUS6: U12.17 (D6), U13.17 (D6)
BUS7: U12.18 (D7), U13.18 (D7)
GND: C10.2, C11.2, C12.2, C13.2, C14.2, C15.2, D1.1 (K), D2.1 (K), D3.1 (K), D4.1 (K), D5.1 (K), D6.1 (K), D7.1 (K), D8.1 (K), D9.1 (K), D10.1 (K), D11.1 (K), D12.1 (K), D13.1 (K), D14.1 (K), D15.1 (K), J4.1, U12.1 (OE), U12.10 (GND), U13.1 (OE), U13.10 (GND), U14.8 (GND), U15.8 (GND), U16.8 (GND), U17.8 (GND)
unnamed: D1.2 (A), R4.2
unnamed: D2.2 (A), R5.2
unnamed: D3.2 (A), R6.2
unnamed: D4.2 (A), R7.2
unnamed: D5.2 (A), R8.2
unnamed: D6.2 (A), R9.2
unnamed: D7.2 (A), R10.2
unnamed: D8.2 (A), R11.2
unnamed: D9.2 (A), R12.2
unnamed: D10.2 (A), R13.2
unnamed: D11.2 (A), R14.2
unnamed: D12.2 (A), R15.2
unnamed: D13.2 (A), R16.2
unnamed: D14.2 (A), R17.2
unnamed: D15.2 (A), R18.2
unnamed: U12.2 (O0), U15.3 (D0)
unnamed: U12.5 (O1), U15.4 (D1)
unnamed: U12.6 (O2), U15.5 (D2)
unnamed: U12.9 (O3), U15.6 (D3)
unnamed: U12.12 (O4), U14.3 (D0)
unnamed: U12.15 (O5), U14.4 (D1)
unnamed: U12.16 (O6), U14.5 (D2)
unnamed: U12.19 (O7), U14.6 (D3)
unnamed: U13.2 (O0), U17.3 (D0)
unnamed: U13.5 (O1), U17.4 (D1)
unnamed: U13.6 (O2), U17.5 (D2)
unnamed: U13.9 (O3), U17.6 (D3)
unnamed: U13.12 (O4), U16.3 (D0)
unnamed: U13.15 (O5), U16.4 (D1)
unnamed: U13.16 (O6), U16.5 (D2)
unnamed: U13.19 (O7), U16.6 (D3)
unnamed: U14.10 (CET), U15.15 (TC)
unnamed: U15.10 (CET), U16.15 (TC)
unnamed: U16.10 (CET), U17.15 (TC)
Phi1: U14.2 (CP), U15.2 (CP), U16.2 (CP), U17.2 (CP)
uA0: J4.2, R4.1, U17.14 (Q0)
uA1: J4.3, R5.1, U17.13 (Q1)
uA2: J4.4, R6.1, U17.12 (Q2)
uA3: J4.5, R7.1, U17.11 (Q3)
uA4: J4.6, R8.1, U16.14 (Q0)
uA5: J4.7, R9.1, U16.13 (Q1)
uA6: J4.8, R10.1, U16.12 (Q2)
uA7: J3.1, R11.1, U15.14 (Q0)
uA8: J3.2, R12.1, U15.13 (Q1)
uA9: J3.3, R13.1, U15.12 (Q2)
uA10: J3.4, R14.1, U15.11 (Q3)
uA11: J3.5, R15.1, U14.14 (Q0)
uA12: J3.6, R16.1, U14.13 (Q1)
uA13: J3.7, R17.1, U14.12 (Q2)
uA14: J3.8, R18.1, U14.11 (Q3)
uH: U12.11 (Cp)
uL: U13.11 (Cp)
~RESET: U14.1 (~MR), U15.1 (~MR), U16.1 (~MR), U17.1 (~MR)
~uLoad: U14.9 (~PE), U15.9 (~PE), U16.9 (~PE), U17.9 (~PE)

Notes on the sheet:
or SN74ALS374N
or SN74LS161AN
H02D-CD-5MM-Kit-100PCS
